Maxim364/-/quartus_project/project/fpga-rtl/ntp_clock.v

module ntp_clock (
    input wire clk,               // Тактовый сигнал (50 МГц)
    input wire reset_n,           // Сброс (активный низкий уровень)
	 input [31:0] HPS_CLOCK,
	 input GPIOdetection,
	 output [9:0] LEDR,
	 output [22:0] GPIO1,
	 output [23:0] GPIO2,
    output wire [6:0] hex2,       // Семисегментный индикатор (минуты, единицы)
    output wire [6:0] hex3,       // Семисегментный индикатор (минуты, десятки)
    output wire [6:0] hex4,       // Семисегментный индикатор (часы, единицы)
    output wire [6:0] hex5,       // Семисегментный индикатор (часы, десятки)
	 output wire [6:0] hex1,
	 output wire [6:0] hex0
);

// Внутренние сигналы для семисегментных индикаторов
	wire [6:0] seg_minutes_units;
	wire [6:0] seg_minutes_tens;
	wire [6:0] seg_hours_units;
	wire [6:0] seg_hours_tens;
	
	wire main_program;


// Преобразуем секунды, минуты и часы в семисегментный код
seven_segment seg_minutes_u (
    .digit( HPS_CLOCK[3:0] ),  // Единицы минут
    .seg(seg_minutes_units)
);

seven_segment seg_minutes_t (
    .digit( HPS_CLOCK[7:4] ),  // Десятки минут
    .seg(seg_minutes_tens)
);

seven_segment seg_hours_u (
    .digit( HPS_CLOCK[11:8] ),    // Единицы часов
    .seg(seg_hours_units)
);

seven_segment seg_hours_t (
    .digit( HPS_CLOCK[15:12] ),    // Десятки часов
    .seg(seg_hours_tens)
);


motion_detector(
    .clk(clk),          // Системный тактовый сигнал
    .motion(GPIOdetection),      // Сигнал от датчика движения
	 .reset(reset_n),
    .main_program(main_program)  // Сигнал для основной программы
);



			motors #(
				.ANGLE(94)
			)seg11(
				 .mclk(clk),
				 .control_input(seg_minutes_units[0]),  //Use this as the control input
				 .reset(reset_n),
				 .main_program(main_program),
				 .servo(GPIO2[0])
				 
			);

			motors #(
				.ANGLE(90)
			)seg12(
				 .mclk(clk),
				 .control_input(seg_minutes_units[1]),  //Use this as the control input
				 .reset(reset_n),
				 .main_program(main_program),
				 .servo(GPIO2[1])	 
			);

			motors #(
				.ANGLE(90)
			)seg13(
				 .mclk(clk),
				 .control_input(seg_minutes_units[2]),  //Use this as the control input
				 .reset(reset_n),
				 .main_program(main_program),
				 .servo(GPIO2[2])
			);

			motors #(
				.ANGLE(97)
			)seg14(
				 .mclk(clk),
				 .control_input(seg_minutes_units[3]),  //Use this as the control input
				 .reset(reset_n),
				 .main_program(main_program),
				 .servo(GPIO2[3])
			);

			motors #(
				.ANGLE(95)
			)seg15(
				 .mclk(clk),
				 .control_input(seg_minutes_units[4]),  //Use this as the control input
				 .reset(reset_n),
				 .main_program(main_program),
				 .servo(GPIO2[4])
			);

			motors #(
				.ANGLE(90)
			)seg16(
				 .mclk(clk),
				 .control_input(seg_minutes_units[5]),  //Use this as the control input
				 .reset(reset_n),
				 .main_program(main_program),
				 .servo(GPIO2[5])
			);


			motors #(
				.ANGLE(90)
			)seg17(
				 .mclk(clk),
				 .control_input(seg_minutes_units[6]),  //Use this as the control input
				 .reset(reset_n),
				 .main_program(main_program),
				 .servo(GPIO2[6])
			);


			motors #(
				.ANGLE(92)
			)seg21(
				 .mclk(clk),
				 .control_input(seg_minutes_tens[0]),  //Use this as the control input
				 .reset(reset_n),
				 .main_program(main_program),
				 .servo(GPIO2[7])
			);


			motors #(
				.ANGLE(90)
			)seg22(
				 .mclk(clk),
				 .control_input(seg_minutes_tens[1]),  //Use this as the control input
				 .reset(reset_n),
				 .main_program(main_program),
				 .servo(GPIO2[8])
			);


			motors #(
				.ANGLE(95)
			)seg23(
				 .mclk(clk),
				 .control_input(seg_minutes_tens[2]),  //Use this as the control input
				 .reset(reset_n),
				 .main_program(main_program),
				 .servo(GPIO2[9])
			);

			motors #(
				.ANGLE(90)
			)seg24(
				 .mclk(clk),
				 .control_input(seg_minutes_tens[3]),  //Use this as the control input
				 .reset(reset_n),
				 .main_program(main_program),
				 .servo(GPIO2[10])
			);

			motors #(
				.ANGLE(92)
			)seg25(
				 .mclk(clk),
				 .control_input(seg_minutes_tens[4]),  //Use this as the control input
				 .reset(reset_n),
				 .main_program(main_program),
				 .servo(GPIO2[11])
			);

			motors #(
				.ANGLE(93)
			)seg26(
				 .mclk(clk),
				 .control_input(seg_minutes_tens[5]),  //Use this as the control input
				 .reset(reset_n),
				 .main_program(main_program),
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
			);


// Назначаем выходные сигналы
assign hex2 = seg_minutes_units;
assign hex3 = seg_minutes_tens;
assign hex4 = seg_hours_units;
assign hex5 = seg_hours_tens;
assign hex1 = 7'b1111111;
assign hex0 = 7'b1111111;
assign LEDR[1] = GPIOdetection;
assign LEDR[2] = main_program;

endmodule
