Maxim364/-/quartus_project/project/fpga-rtl/soc_system/soc_system_inst.vhd

	component soc_system is
		port (
			clk_clk                               : in    std_logic                     := 'X';             -- clk
			reset_reset_n                         : in    std_logic                     := 'X';             -- reset_n
			memory_mem_a                          : out   std_logic_vector(14 downto 0);                    -- mem_a
			memory_mem_ba                         : out   std_logic_vector(2 downto 0);                     -- mem_ba
			memory_mem_ck                         : out   std_logic;                                        -- mem_ck
			memory_mem_ck_n                       : out   std_logic;                                        -- mem_ck_n
			memory_mem_cke                        : out   std_logic;                                        -- mem_cke
			memory_mem_cs_n                       : out   std_logic;                                        -- mem_cs_n
			memory_mem_ras_n                      : out   std_logic;                                        -- mem_ras_n
			memory_mem_cas_n                      : out   std_logic;                                        -- mem_cas_n
			memory_mem_we_n                       : out   std_logic;                                        -- mem_we_n
			memory_mem_reset_n                    : out   std_logic;                                        -- mem_reset_n
			memory_mem_dq                         : inout std_logic_vector(31 downto 0) := (others => 'X'); -- mem_dq
			memory_mem_dqs                        : inout std_logic_vector(3 downto 0)  := (others => 'X'); -- mem_dqs
			memory_mem_dqs_n                      : inout std_logic_vector(3 downto 0)  := (others => 'X'); -- mem_dqs_n
			memory_mem_odt                        : out   std_logic;                                        -- mem_odt
			memory_mem_dm                         : out   std_logic_vector(3 downto 0);                     -- mem_dm
			memory_oct_rzqin                      : in    std_logic                     := 'X';             -- oct_rzqin
			hps_0_hps_io_hps_io_emac1_inst_TX_CLK : out   std_logic;                                        -- hps_io_emac1_inst_TX_CLK
			hps_0_hps_io_hps_io_emac1_inst_TXD0   : out   std_logic;                                        -- hps_io_emac1_inst_TXD0
			hps_0_hps_io_hps_io_emac1_inst_TXD1   : out   std_logic;                                        -- hps_io_emac1_inst_TXD1
			hps_0_hps_io_hps_io_emac1_inst_TXD2   : out   std_logic;                                        -- hps_io_emac1_inst_TXD2
			hps_0_hps_io_hps_io_emac1_inst_TXD3   : out   std_logic;                                        -- hps_io_emac1_inst_TXD3
			hps_0_hps_io_hps_io_emac1_inst_RXD0   : in    std_logic                     := 'X';             -- hps_io_emac1_inst_RXD0
			hps_0_hps_io_hps_io_emac1_inst_MDIO   : inout std_logic                     := 'X';             -- hps_io_emac1_inst_MDIO
			hps_0_hps_io_hps_io_emac1_inst_MDC    : out   std_logic;                                        -- hps_io_emac1_inst_MDC
			hps_0_hps_io_hps_io_emac1_inst_RX_CTL : in    std_logic                     := 'X';             -- hps_io_emac1_inst_RX_CTL
			hps_0_hps_io_hps_io_emac1_inst_TX_CTL : out   std_logic;                                        -- hps_io_emac1_inst_TX_CTL
			hps_0_hps_io_hps_io_emac1_inst_RX_CLK : in    std_logic                     := 'X';             -- hps_io_emac1_inst_RX_CLK
			hps_0_hps_io_hps_io_emac1_inst_RXD1   : in    std_logic                     := 'X';             -- hps_io_emac1_inst_RXD1
			hps_0_hps_io_hps_io_emac1_inst_RXD2   : in    std_logic                     := 'X';             -- hps_io_emac1_inst_RXD2
			hps_0_hps_io_hps_io_emac1_inst_RXD3   : in    std_logic                     := 'X';             -- hps_io_emac1_inst_RXD3
			hps_0_hps_io_hps_io_qspi_inst_IO0     : inout std_logic                     := 'X';             -- hps_io_qspi_inst_IO0
			hps_0_hps_io_hps_io_qspi_inst_IO1     : inout std_logic                     := 'X';             -- hps_io_qspi_inst_IO1
			hps_0_hps_io_hps_io_qspi_inst_IO2     : inout std_logic                     := 'X';             -- hps_io_qspi_inst_IO2
			hps_0_hps_io_hps_io_qspi_inst_IO3     : inout std_logic                     := 'X';             -- hps_io_qspi_inst_IO3
			hps_0_hps_io_hps_io_qspi_inst_SS0     : out   std_logic;                                        -- hps_io_qspi_inst_SS0
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
			hps_0_hps_io_hps_io_gpio_inst_GPIO54  : inout std_logic                     := 'X';             -- hps_io_gpio_inst_GPIO54
			hps_0_hps_io_hps_io_gpio_inst_GPIO61  : inout std_logic                     := 'X';             -- hps_io_gpio_inst_GPIO61
			hps_0_h2f_reset_reset_n               : out   std_logic;                                        -- reset_n
			hps_0_f2h_stm_hw_events_stm_hwevents  : in    std_logic_vector(27 downto 0) := (others => 'X'); -- stm_hwevents
			hps_0_f2h_warm_reset_req_reset_n      : in    std_logic                     := 'X';             -- reset_n
			hps_0_f2h_debug_reset_req_reset_n     : in    std_logic                     := 'X';             -- reset_n
			hps_0_f2h_cold_reset_req_reset_n      : in    std_logic                     := 'X';             -- reset_n
			pio_led_external_connection_export    : out   std_logic_vector(31 downto 0)                     -- export
		);
	end component soc_system;

	u0 : component soc_system
		port map (
			clk_clk                               => CONNECTED_TO_clk_clk,                               --                         clk.clk
			reset_reset_n                         => CONNECTED_TO_reset_reset_n,                         --                       reset.reset_n
			memory_mem_a                          => CONNECTED_TO_memory_mem_a,                          --                      memory.mem_a
			memory_mem_ba                         => CONNECTED_TO_memory_mem_ba,                         --                            .mem_ba
			memory_mem_ck                         => CONNECTED_TO_memory_mem_ck,                         --                            .mem_ck
			memory_mem_ck_n                       => CONNECTED_TO_memory_mem_ck_n,                       --                            .mem_ck_n
			memory_mem_cke                        => CONNECTED_TO_memory_mem_cke,                        --                            .mem_cke
			memory_mem_cs_n                       => CONNECTED_TO_memory_mem_cs_n,                       --                            .mem_cs_n
			memory_mem_ras_n                      => CONNECTED_TO_memory_mem_ras_n,                      --                            .mem_ras_n
			memory_mem_cas_n                      => CONNECTED_TO_memory_mem_cas_n,                      --                            .mem_cas_n
			memory_mem_we_n                       => CONNECTED_TO_memory_mem_we_n,                       --                            .mem_we_n
			memory_mem_reset_n                    => CONNECTED_TO_memory_mem_reset_n,                    --                            .mem_reset_n
			memory_mem_dq                         => CONNECTED_TO_memory_mem_dq,                         --                            .mem_dq
			memory_mem_dqs                        => CONNECTED_TO_memory_mem_dqs,                        --                            .mem_dqs
			memory_mem_dqs_n                      => CONNECTED_TO_memory_mem_dqs_n,                      --                            .mem_dqs_n
			memory_mem_odt                        => CONNECTED_TO_memory_mem_odt,                        --                            .mem_odt
			memory_mem_dm                         => CONNECTED_TO_memory_mem_dm,                         --                            .mem_dm
			memory_oct_rzqin                      => CONNECTED_TO_memory_oct_rzqin,                      --                            .oct_rzqin
			hps_0_hps_io_hps_io_emac1_inst_TX_CLK => CONNECTED_TO_hps_0_hps_io_hps_io_emac1_inst_TX_CLK, --                hps_0_hps_io.hps_io_emac1_inst_TX_CLK
			hps_0_hps_io_hps_io_emac1_inst_TXD0   => CONNECTED_TO_hps_0_hps_io_hps_io_emac1_inst_TXD0,   --                            .hps_io_emac1_inst_TXD0
			hps_0_hps_io_hps_io_emac1_inst_TXD1   => CONNECTED_TO_hps_0_hps_io_hps_io_emac1_inst_TXD1,   --                            .hps_io_emac1_inst_TXD1
			hps_0_hps_io_hps_io_emac1_inst_TXD2   => CONNECTED_TO_hps_0_hps_io_hps_io_emac1_inst_TXD2,   --                            .hps_io_emac1_inst_TXD2
			hps_0_hps_io_hps_io_emac1_inst_TXD3   => CONNECTED_TO_hps_0_hps_io_hps_io_emac1_inst_TXD3,   --                            .hps_io_emac1_inst_TXD3
			hps_0_hps_io_hps_io_emac1_inst_RXD0   => CONNECTED_TO_hps_0_hps_io_hps_io_emac1_inst_RXD0,   --                            .hps_io_emac1_inst_RXD0
			hps_0_hps_io_hps_io_emac1_inst_MDIO   => CONNECTED_TO_hps_0_hps_io_hps_io_emac1_inst_MDIO,   --                            .hps_io_emac1_inst_MDIO
			hps_0_hps_io_hps_io_emac1_inst_MDC    => CONNECTED_TO_hps_0_hps_io_hps_io_emac1_inst_MDC,    --                            .hps_io_emac1_inst_MDC
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
			hps_0_hps_io_hps_io_usb1_inst_DIR     => CONNECTED_TO_hps_0_hps_io_hps_io_usb1_inst_DIR,     --                            .hps_io_usb1_inst_DIR
			hps_0_hps_io_hps_io_usb1_inst_NXT     => CONNECTED_TO_hps_0_hps_io_hps_io_usb1_inst_NXT,     --                            .hps_io_usb1_inst_NXT
			hps_0_hps_io_hps_io_spim1_inst_CLK    => CONNECTED_TO_hps_0_hps_io_hps_io_spim1_inst_CLK,    --                            .hps_io_spim1_inst_CLK
			hps_0_hps_io_hps_io_spim1_inst_MOSI   => CONNECTED_TO_hps_0_hps_io_hps_io_spim1_inst_MOSI,   --                            .hps_io_spim1_inst_MOSI
			hps_0_hps_io_hps_io_spim1_inst_MISO   => CONNECTED_TO_hps_0_hps_io_hps_io_spim1_inst_MISO,   --                            .hps_io_spim1_inst_MISO
			hps_0_hps_io_hps_io_spim1_inst_SS0    => CONNECTED_TO_hps_0_hps_io_hps_io_spim1_inst_SS0,    --                            .hps_io_spim1_inst_SS0
			hps_0_hps_io_hps_io_uart0_inst_RX     => CONNECTED_TO_hps_0_hps_io_hps_io_uart0_inst_RX,     --                            .hps_io_uart0_inst_RX
			hps_0_hps_io_hps_io_uart0_inst_TX     => CONNECTED_TO_hps_0_hps_io_hps_io_uart0_inst_TX,     --                            .hps_io_uart0_inst_TX
			hps_0_hps_io_hps_io_i2c0_inst_SDA     => CONNECTED_TO_hps_0_hps_io_hps_io_i2c0_inst_SDA,     --                            .hps_io_i2c0_inst_SDA
			hps_0_hps_io_hps_io_i2c0_inst_SCL     => CONNECTED_TO_hps_0_hps_io_hps_io_i2c0_inst_SCL,     --                            .hps_io_i2c0_inst_SCL
			hps_0_hps_io_hps_io_i2c1_inst_SDA     => CONNECTED_TO_hps_0_hps_io_hps_io_i2c1_inst_SDA,     --                            .hps_io_i2c1_inst_SDA
			hps_0_hps_io_hps_io_i2c1_inst_SCL     => CONNECTED_TO_hps_0_hps_io_hps_io_i2c1_inst_SCL,     --                            .hps_io_i2c1_inst_SCL
			hps_0_hps_io_hps_io_gpio_inst_GPIO09  => CONNECTED_TO_hps_0_hps_io_hps_io_gpio_inst_GPIO09,  --                            .hps_io_gpio_inst_GPIO09
			hps_0_hps_io_hps_io_gpio_inst_GPIO35  => CONNECTED_TO_hps_0_hps_io_hps_io_gpio_inst_GPIO35,  --                            .hps_io_gpio_inst_GPIO35
			hps_0_hps_io_hps_io_gpio_inst_GPIO40  => CONNECTED_TO_hps_0_hps_io_hps_io_gpio_inst_GPIO40,  --                            .hps_io_gpio_inst_GPIO40
			hps_0_hps_io_hps_io_gpio_inst_GPIO48  => CONNECTED_TO_hps_0_hps_io_hps_io_gpio_inst_GPIO48,  --                            .hps_io_gpio_inst_GPIO48
			hps_0_hps_io_hps_io_gpio_inst_GPIO53  => CONNECTED_TO_hps_0_hps_io_hps_io_gpio_inst_GPIO53,  --                            .hps_io_gpio_inst_GPIO53
			hps_0_hps_io_hps_io_gpio_inst_GPIO54  => CONNECTED_TO_hps_0_hps_io_hps_io_gpio_inst_GPIO54,  --                            .hps_io_gpio_inst_GPIO54
			hps_0_hps_io_hps_io_gpio_inst_GPIO61  => CONNECTED_TO_hps_0_hps_io_hps_io_gpio_inst_GPIO61,  --                            .hps_io_gpio_inst_GPIO61
			hps_0_h2f_reset_reset_n               => CONNECTED_TO_hps_0_h2f_reset_reset_n,               --             hps_0_h2f_reset.reset_n
			hps_0_f2h_stm_hw_events_stm_hwevents  => CONNECTED_TO_hps_0_f2h_stm_hw_events_stm_hwevents,  --     hps_0_f2h_stm_hw_events.stm_hwevents
			hps_0_f2h_warm_reset_req_reset_n      => CONNECTED_TO_hps_0_f2h_warm_reset_req_reset_n,      --    hps_0_f2h_warm_reset_req.reset_n
			hps_0_f2h_debug_reset_req_reset_n     => CONNECTED_TO_hps_0_f2h_debug_reset_req_reset_n,     --   hps_0_f2h_debug_reset_req.reset_n
			hps_0_f2h_cold_reset_req_reset_n      => CONNECTED_TO_hps_0_f2h_cold_reset_req_reset_n,      --    hps_0_f2h_cold_reset_req.reset_n
			pio_led_external_connection_export    => CONNECTED_TO_pio_led_external_connection_export     -- pio_led_external_connection.export
		);
