Maxim364/-/quartus_project/project/fpga-rtl/seven_segment.v

module seven_segment (
    input wire [3:0] digit,  // Вход: цифра (0–9)
    output reg [6:0] seg     // Выход: семисегментный код
);

always @(*) begin
    case (digit)
        4'h0: seg = 7'b1000000;  // 0
        4'h1: seg = 7'b1111001;  // 1
        4'h2: seg = 7'b0100100;  // 2
        4'h3: seg = 7'b0110000;  // 3
        4'h4: seg = 7'b0011001;  // 4
        4'h5: seg = 7'b0010010;  // 5
        4'h6: seg = 7'b0000010;  // 6
        4'h7: seg = 7'b1111000;  // 7
        4'h8: seg = 7'b0000000;  // 8
        4'h9: seg = 7'b0010000;  // 9
        default: seg = 7'b1111111;  // Пусто
    endcase
end

endmodule
